Resaj/speed-demon/images/DSCF2870.jpg

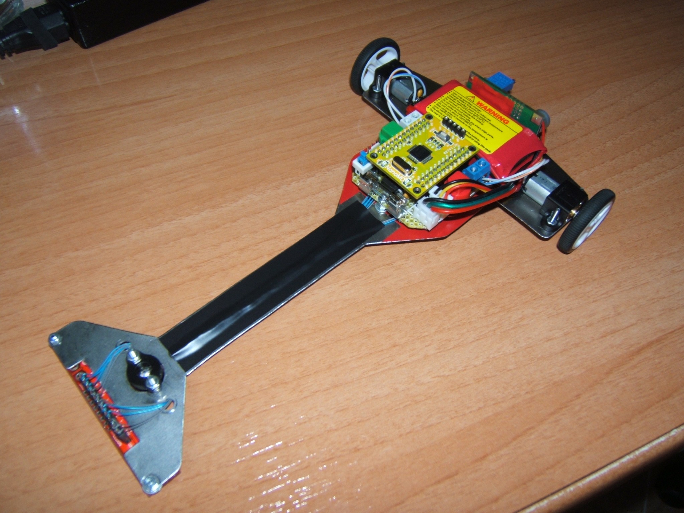
images/DSCF2870.jpg
