Resaj/speed-demon/images/DSCF2871.JPG

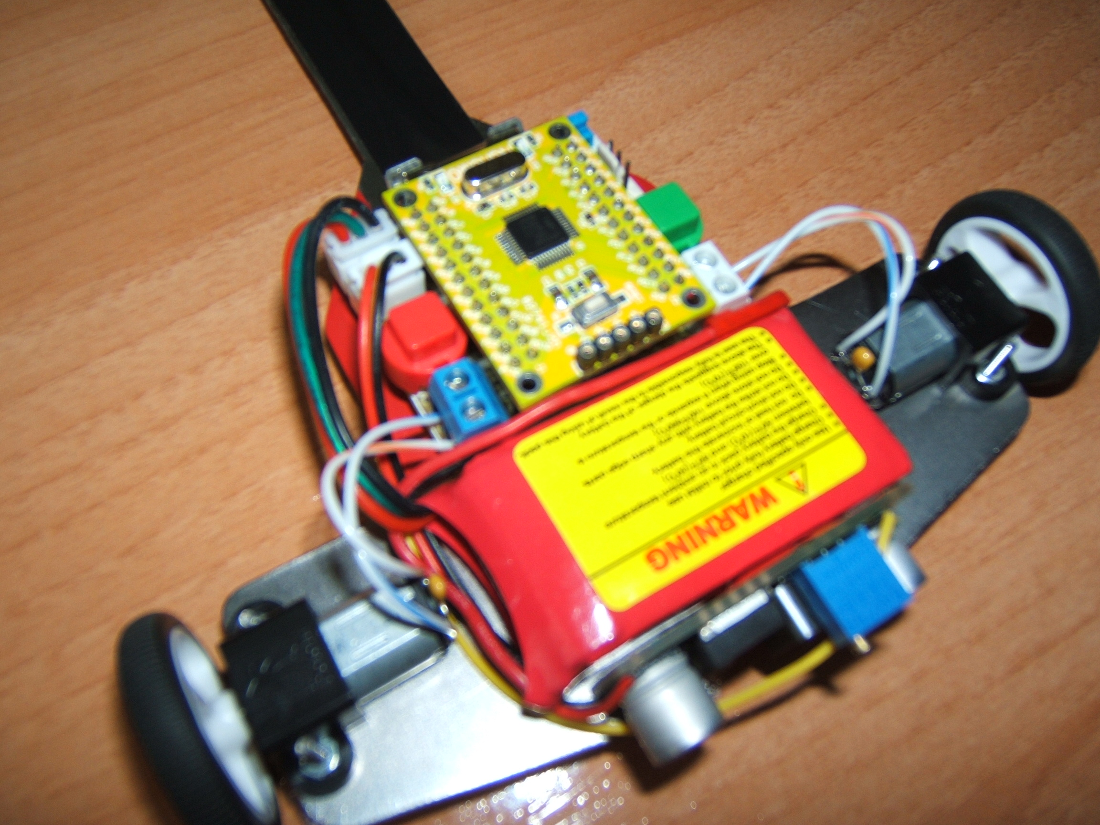
images/DSCF2871.JPG
