Resaj/speed-demon/images/DSCF2872.JPG

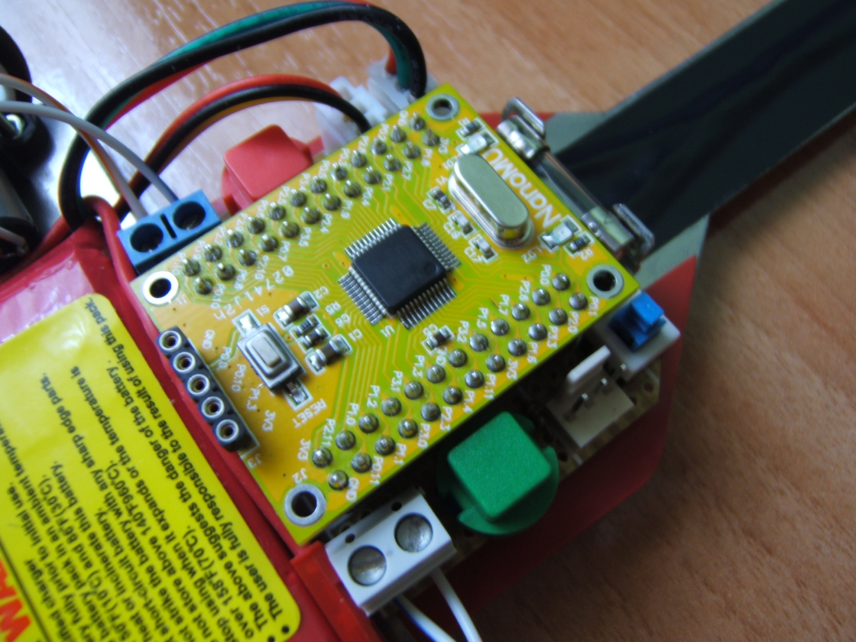
images/DSCF2872.JPG
