Resaj/speed-demon/images/DSCF2874.JPG

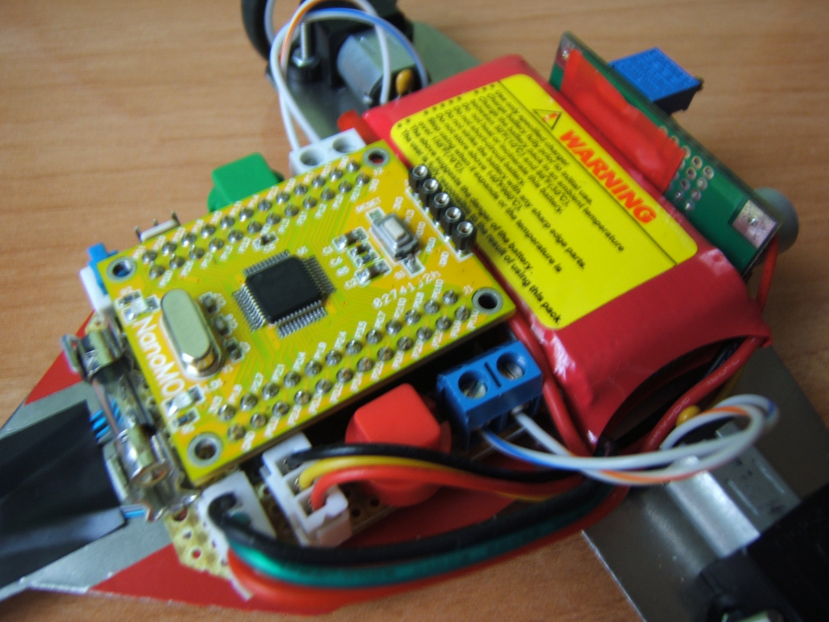
images/DSCF2874.JPG
