Resaj/speed-demon/images/DSCF2875.JPG

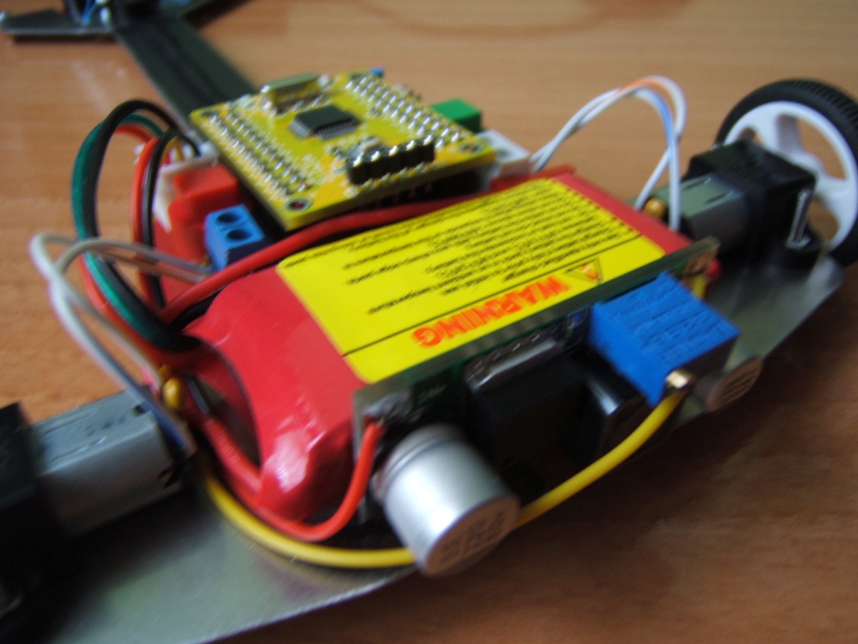
images/DSCF2875.JPG
