Resaj/speed-demon/images/DSCF2878.jpg

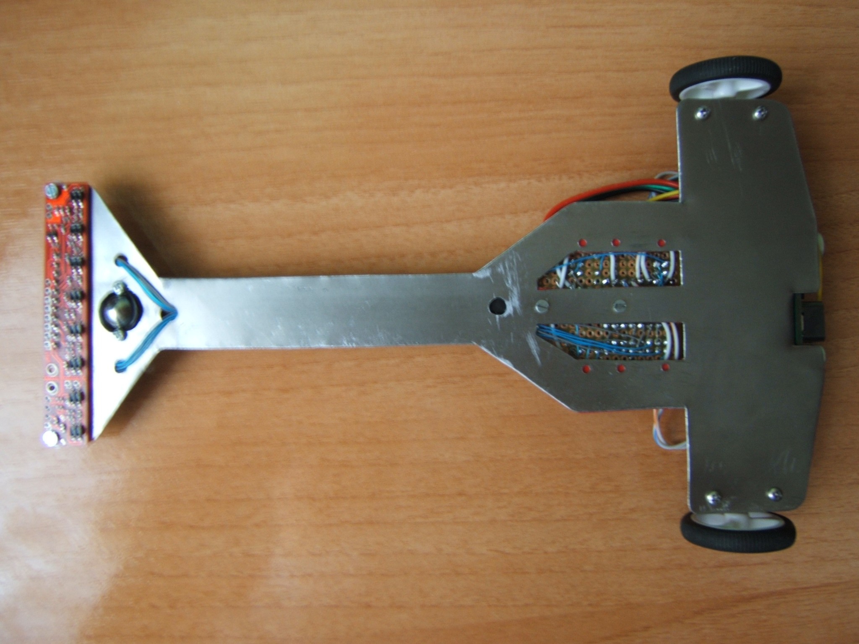
images/DSCF2878.jpg
