Resaj/speed-demon/images/DSCF2879.JPG

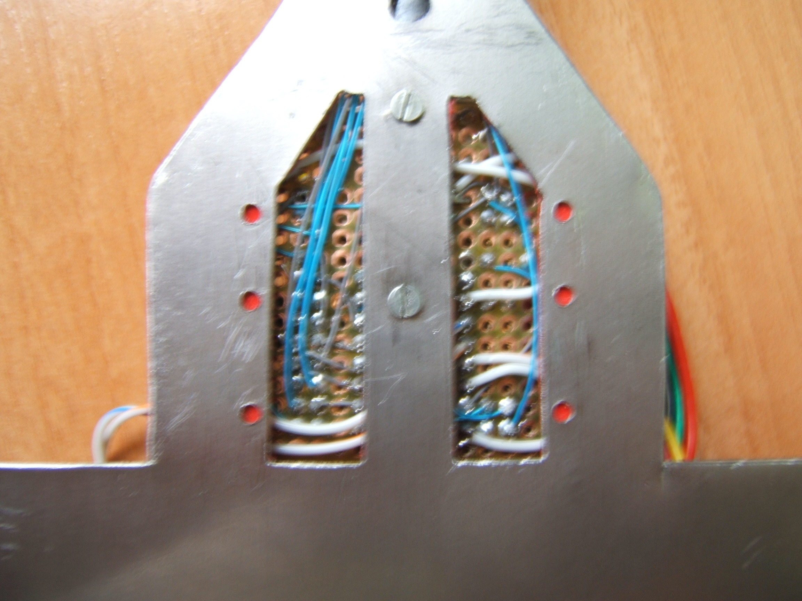
images/DSCF2879.JPG
