Resaj/speed-demon/images/DSCF2881.JPG

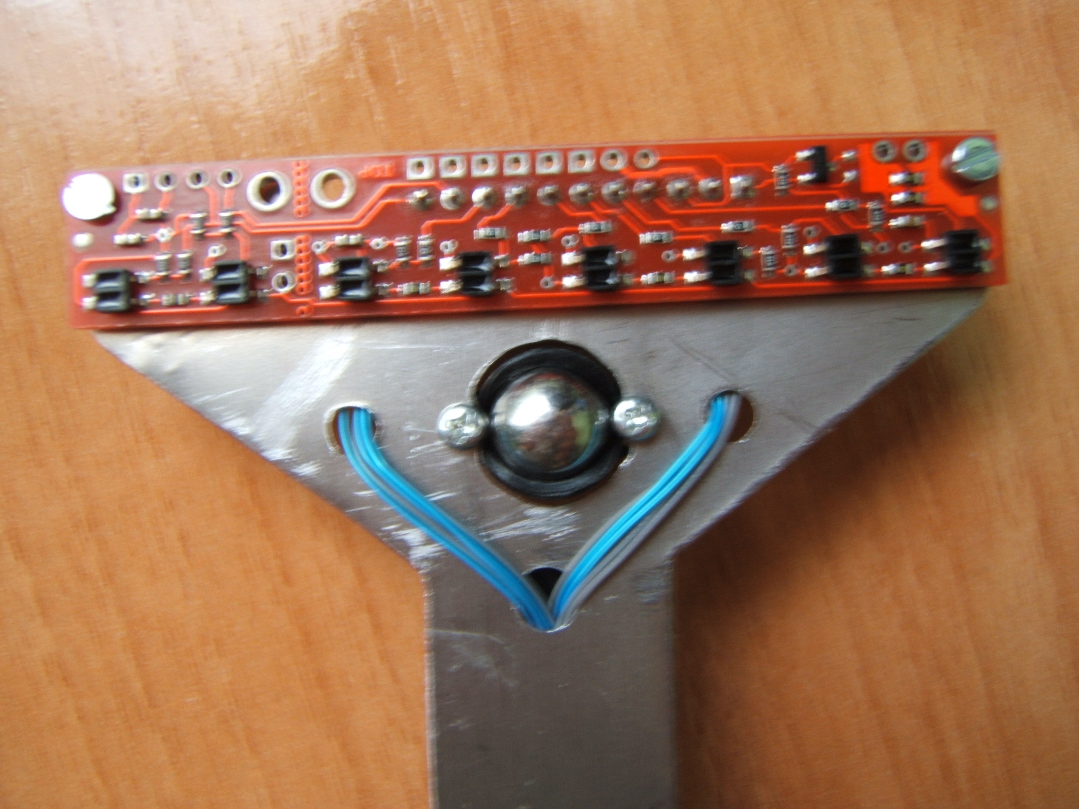
images/DSCF2881.JPG
