Resaj/speed-demon/images/DSCF2887.JPG

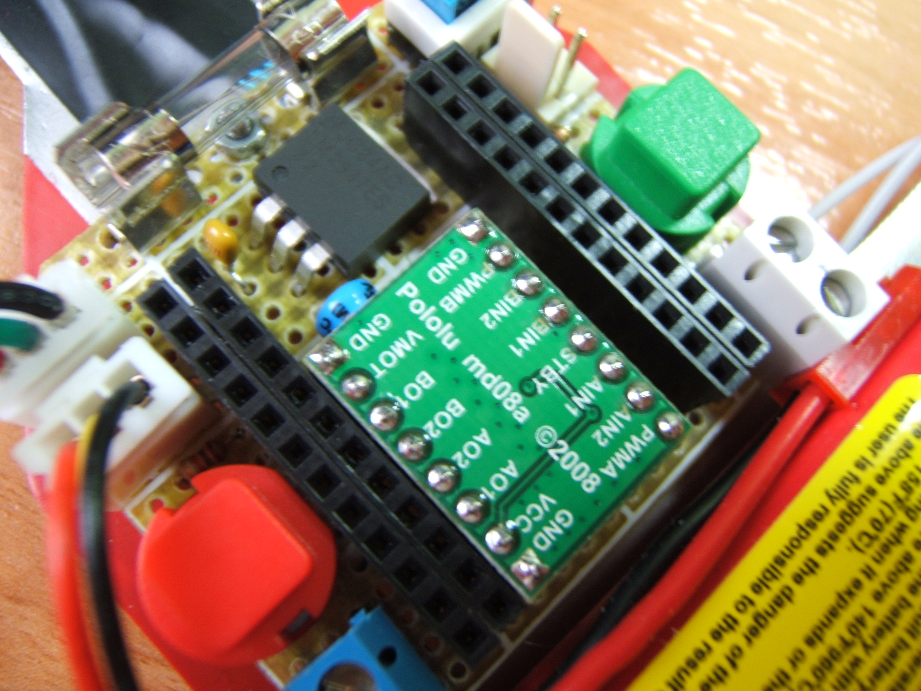
images/DSCF2887.JPG
