Resaj/speed-demon/images/DSCF2888.JPG

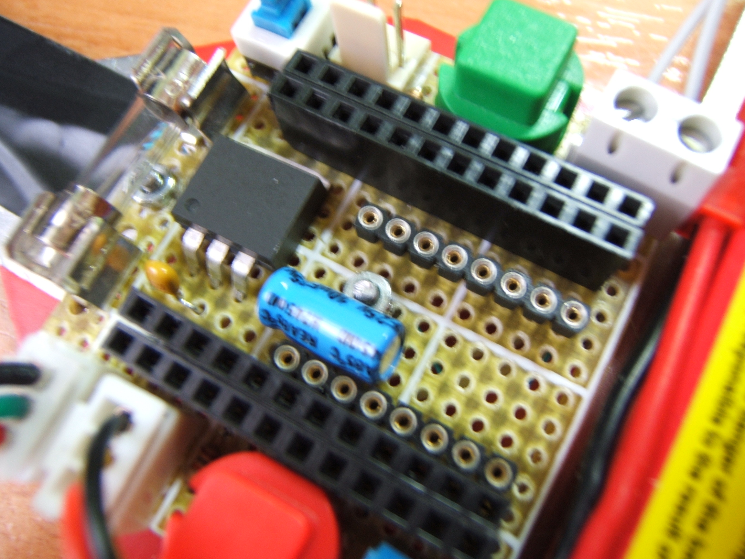
images/DSCF2888.JPG
