Resaj/speed-demon/images/DSCF2895.jpg

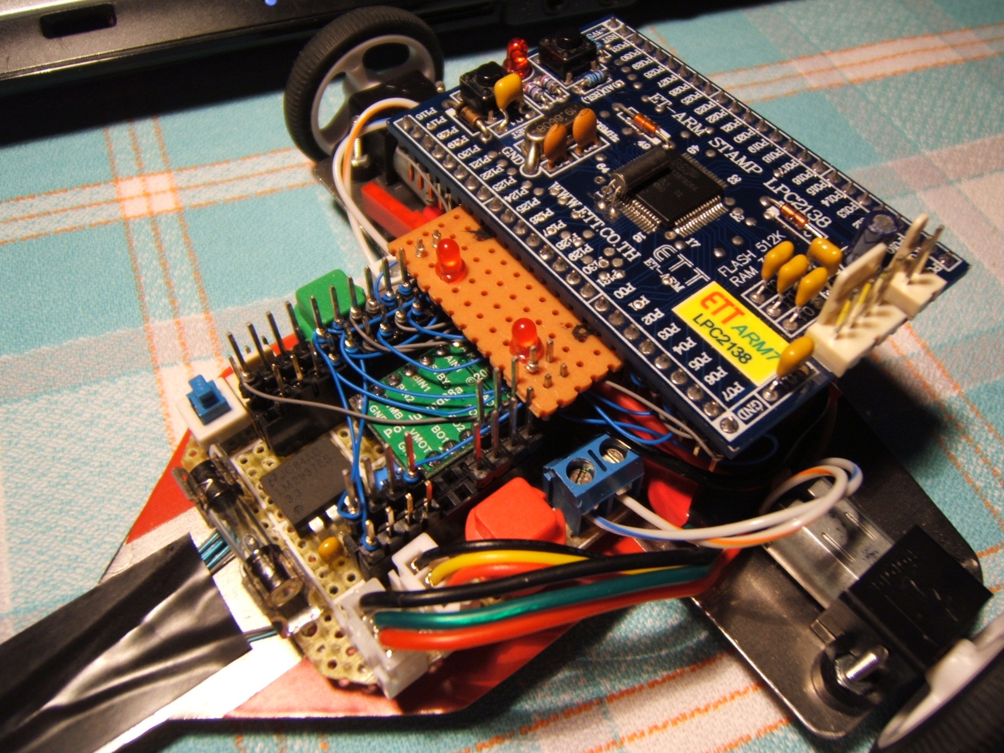
images/DSCF2895.jpg
