Resaj/speed-demon/images/DSCF3370.jpg

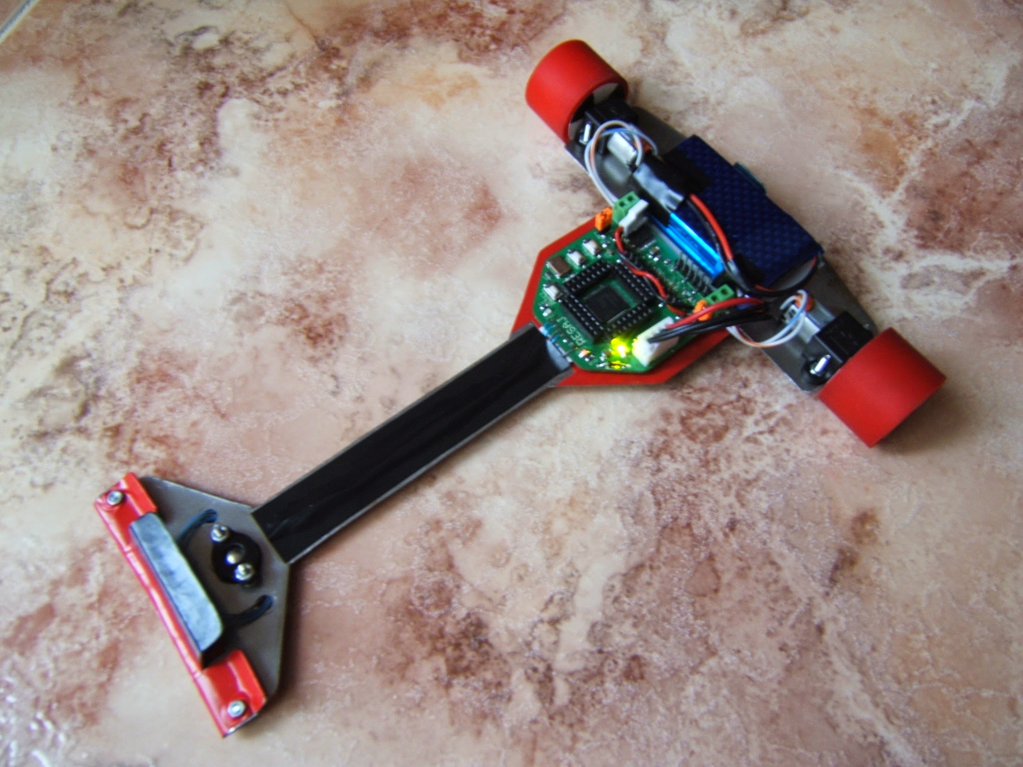
images/DSCF3370.jpg
