Resaj/speed-demon/software/Programa velocista (beta)/LPClib.c

#ifndef LPCLIB_C
#define LPCLIB_C

#include <lpc213x.h>
#include "LPClib.h"
#include "target.h"


void ADC_CH_config(struct analog data_adc)
{
	struct data data_pin;
	data_pin.port = 0;

	if(data_adc.adc == ADC_0)
	{
		switch(data_adc.channel)
		{
			case ADC_CH0:
				data_pin.pin = 27;
				PINSEL_config(data_pin, ADC);
				break;
			case ADC_CH1:
				data_pin.pin = 28;
				PINSEL_config(data_pin, ADC);
				break;
			case ADC_CH2:
				data_pin.pin = 29;
				PINSEL_config(data_pin, ADC);
				break;
			case ADC_CH3:
				data_pin.pin = 30;
				PINSEL_config(data_pin, ADC);
				break;
			case ADC_CH4:
				data_pin.pin = 25;
				PINSEL_config(data_pin, ADC);
				break;
			case ADC_CH5:
				data_pin.pin = 26;
				PINSEL_config(data_pin, ADC);
				break;
			case ADC_CH6:
				data_pin.pin = 4;
				PINSEL_config(data_pin, ADC);
				break;
			case ADC_CH7:
				data_pin.pin = 5;
				PINSEL_config(data_pin, ADC);
		}
	}
	else if(data_adc.adc == ADC_1)
	{
		switch(data_adc.channel)
		{
			case ADC_CH0:
				data_pin.pin = 6;
				PINSEL_config(data_pin, ADC);
				break;
			case ADC_CH1:
				data_pin.pin = 8;
				PINSEL_config(data_pin, ADC);
				break;
			case ADC_CH2:
				data_pin.pin = 10;
				PINSEL_config(data_pin, ADC);
				break;
			case ADC_CH3:
				data_pin.pin = 12;
				PINSEL_config(data_pin, ADC);
				break;
			case ADC_CH4:
				data_pin.pin = 13;
				PINSEL_config(data_pin, ADC);
				break;
			case ADC_CH5:
				data_pin.pin = 15;
				PINSEL_config(data_pin, ADC);
				break;
			case ADC_CH6:
				data_pin.pin = 21;
				PINSEL_config(data_pin, ADC);
				break;
			case ADC_CH7:
				data_pin.pin = 22;
				PINSEL_config(data_pin, ADC);
		}
	}
}

void ADC_enable(int adc)
{
	if(adc == ADC_0)
		AD0CR = 0x200000;
	else if(adc == ADC_1)
		AD1CR = 0x200000;
}

unsigned int ADC_read(struct analog data_adc)
{
	unsigned int value = 0;

	if(data_adc.adc == ADC_0)
	{
		AD0CR |= (1<<24)|(1<<data_adc.channel);
		while ((AD0DR&(1<<31))==0);
		AD0CR &= ~((1<<24)|(1<<data_adc.channel));
		value = (AD0DR>>6)&0x03FF;
	}
	else if(data_adc.adc == ADC_1)
	{
		AD1CR |= (1<<24)|(1<<data_adc.channel);
		while ((AD1DR&(1<<31))==0);
		AD1CR &= ~((1<<24)|(1<<data_adc.channel));
		value = (AD1DR>>6)&0x03FF;
	}

	return value;
}

char BUTTON_status(struct data button_data_pin)
{
	char var = GPIO_read(button_data_pin);

	if(var == '0')
		return '1';
	else // var = '1'
		return '0';
}

unsigned int GP2Y0A_read(struct analog data_adc)
{
	unsigned int adc_value, distance_value;

	adc_value = ADC_read(data_adc);

	if(adc_value > 23)
		distance_value = 25*((3000.0 / (adc_value - 23) + 0.3)); // Fórmula de conversión de tensión a mm.
	else
		distance_value = 800;

	if (distance_value > 800)
		distance_value = 800;
	else if (distance_value < 100)
		distance_value = 100;

	return distance_value;
}

unsigned int GP2D120_read(struct analog data_adc)
{
	unsigned int adc_value, distance_value;

	adc_value = ADC_read(data_adc);

	distance_value = 16.8*((2914.0 / (adc_value + 35) - 0.5)); // Fórmula de conversión de tensión a mm.

	if (distance_value > 350)
		distance_value = 350;
	else if (distance_value < 40)
		distance_value = 40;

	return distance_value;
}

char DISTANCE_digital_read(struct data sensor_data_pin)
{
	char var = GPIO_read(sensor_data_pin);

	if(var == '0')
		return '1';
	else // var = '1'
		return '0';
}

void EINT_config(struct data data_pin, char mode, char polar, unsigned int priority)
{
	int ext_int;
	unsigned int int_num;
	unsigned long name;

	if(data_pin.port == 0)
	{
		switch(data_pin.pin)
		{
			case 1:
				ext_int = 0;
				break;
			case 3:
				ext_int = 1;
				break;
			case 7:
				ext_int = 2;
				break;
			case 9:
				ext_int = 3;
				break;
			case 14:
				ext_int = 1;
				break;
			case 15:
				ext_int = 2;
				break;
			case 16:
				ext_int = 2;
				break;
			case 20:
				ext_int = 3;
				break;
			case 30:
				ext_int = 3;
		}
	}

	switch(ext_int)
	{
		case 0:
			int_num = 14;
			name = (unsigned long) EINT_0;
			break;
		case 1:
			int_num = 15;
			name = (unsigned long) EINT_1;
			break;
		case 2:
			int_num = 16;
			name = (unsigned long) EINT_2;
			break;
		default: // ext_int = 3
			int_num = 17;
			name = (unsigned long) EINT_3;
	}

	if(mode == LEVEL)
		EXTMODE &= ~(1<<ext_int);
	else // mode = EDGE
		EXTMODE |= 1<<ext_int;

	if(polar == DOWN)
		EXTPOLAR &= ~(1<<ext_int);
	else // polar = UP
		EXTPOLAR |= 1<<ext_int;

	PINSEL_config(data_pin, EINT);
	VIC_assign(name, priority, int_num);
}

float ENCODER_distance(float diameter, int edge_num, int cont)
{
	float distance;
	distance = pi * diameter * cont / edge_num;

	return distance;
}

float ENCODER_speed(float diameter, int edge_num, float time)
{
	float speed;

	speed = pi * diameter / (1000 * edge_num * time);

	return speed;
}

void GPIO_config(struct data data_pin, char inout)
{
	if(inout == IN)
	{
		if(data_pin.port == 0)
			IO0DIR &= ~(1<<data_pin.pin);
		else // port = 1
			IO1DIR &= ~(1<<data_pin.pin);
	}
	else // inout = OUT
	{
		if(data_pin.port == 0)
			IO0DIR |= 1<<data_pin.pin;
		else // port = 1
			IO1DIR |= 1<<data_pin.pin;
	}
}

void GPIO_set(struct data data_pin, unsigned char status)
{
	if(status == PIN_OFF)
	{
		if(data_pin.port == 0)
			IOCLR0 = 1<<data_pin.pin;
		else // port = 1
			IOCLR1 = 1<<data_pin.pin;
	}
	else // status = PIN_ON
	{
		if(data_pin.port == 0)
			IOSET0 = 1<<data_pin.pin;
		else // port = 1
			IOSET1 = 1<<data_pin.pin;
	}		
}

char GPIO_read(struct data data_pin)
{
	if(data_pin.port == 0)
	{
		if((IO0PIN&(1<<data_pin.pin)) == 0)
			return '0';
		else
			return '1';
	}
	else // port = 1
	{
		if((IO1PIN&(1<<data_pin.pin)) == 0)
			return '0';
		else
			return '1';
	}
}

void LED_set(struct data led_data_pin, unsigned char status)
{
	GPIO_set(led_data_pin, status);
}

unsigned int LINE_SENSOR_read(struct analog data_adc)
{
	unsigned int value;
	value = ADC_read(data_adc);
	return value;
}

char LIPO_TENSION_read(struct analog data_adc, float v_min)
{
	unsigned int value;
	value = ADC_read(data_adc);

	if(value < v_min*1024/3.3)
		return '1';
	else
		return '0';
}

void MOTOR_config(struct motor MOTOR)
{
	GPIO_config(MOTOR.bridge_h_pos_data_pin, OUT);
	GPIO_config(MOTOR.bridge_h_neg_data_pin, OUT);

	PWM_CH_config(MOTOR.channel);
}

void MOTOR_SPEED_set(struct motor MOTOR, float speed, char mode)
{
	if(mode == FORWARD)
	{
		GPIO_set(MOTOR.bridge_h_pos_data_pin, PIN_ON);
		GPIO_set(MOTOR.bridge_h_neg_data_pin, PIN_OFF);
	}
	else if(mode == BACKWARD)
	{
		GPIO_set(MOTOR.bridge_h_pos_data_pin, PIN_OFF);
		GPIO_set(MOTOR.bridge_h_neg_data_pin, PIN_ON);
	}
	else if(mode == LOCKED)
	{
		GPIO_set(MOTOR.bridge_h_pos_data_pin, PIN_ON);
		GPIO_set(MOTOR.bridge_h_neg_data_pin, PIN_ON);
	}
	else // mode == FREE
	{
		GPIO_set(MOTOR.bridge_h_pos_data_pin, PIN_OFF);
		GPIO_set(MOTOR.bridge_h_neg_data_pin, PIN_OFF);
	}

	PWM_set(MOTOR.channel, speed);
}

void PINSEL_config(struct data data_pin, char mode)
{
	if(data_pin.port == 0)
	{
		switch(data_pin.pin)
		{
			case 0:
				switch(mode)
				{
					case UART:
						PINSEL0 |= 1<<0;
						break;
					case PWM:
						PINSEL0 |= 2<<0;
				}
				break;
			case 1:
				switch(mode)
				{
					case UART:
						PINSEL0 |= 1<<2;
						break;
					case PWM:
						PINSEL0 |= 2<<2;
						break;
					case EINT:
						PINSEL0 |= 3<<2;
				}
				break;
			case 2:
				switch(mode)
				{
					case I2C:
						PINSEL0 |= 1<<4;
						break;
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
			break;
		case 13:
			VICVectAddr13 = name;
			VICVectCntl13 = (0x20|num);
			break;
		case 14:
			VICVectAddr14 = name;
			VICVectCntl14 = (0x20|num);
			break;
		default: // priority = 15
			VICVectAddr15 = name;
			VICVectCntl15 = (0x20|num);
	}

	VICIntEnable |= 1<<num;
}


#endif
