Resaj/speed-demon/software/Programa velocista (beta)/target.h

#ifndef TARGET_H
#define TARGET_H

#define Fpclk 		19.6608e6*3/4	// Frecuencia del cristal del LPC2138
#define PWM_PERIOD	1e-5			// Periodo de PWM
#define BAT_PERIOD	5				// Periodo de ejecución de la interrupción periódica de la batería
#define PER_PERIOD	5e-3			// Periodo de ejecución de la interrupción periódica principal

#endif
